Tinkerforge/industrial-dual-ac-in-bricklet/software/src/communication.h

/* industrial-dual-ac-in-bricklet
 * Copyright (C) 2023 Olaf Lüke <olaf@tinkerfoe.com>
 *
 * communication.h: TFP protocol message handling
 *
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
 * You should have received a copy of the GNU Lesser General Public
 * License along with this library; if not, write to the
 * Free Software Foundation, Inc., 59 Temple Place - Suite 330,
 * Boston, MA 02111-1307, USA.
 */

#ifndef COMMUNICATION_H
#define COMMUNICATION_H

#include <stdint.h>
#include <stdbool.h>

#include "bricklib2/protocols/tfp/tfp.h"
#include "bricklib2/bootloader/bootloader.h"

// Default functions
BootloaderHandleMessageResponse handle_message(const void *data, void *response);
void communication_tick(void);
void communication_init(void);

// Constants

#define INDUSTRIAL_DUAL_AC_IN_CHANNEL_0 0
#define INDUSTRIAL_DUAL_AC_IN_CHANNEL_1 1

#define INDUSTRIAL_DUAL_AC_IN_CHANNEL_LED_CONFIG_OFF 0
#define INDUSTRIAL_DUAL_AC_IN_CHANNEL_LED_CONFIG_ON 1
#define INDUSTRIAL_DUAL_AC_IN_CHANNEL_LED_CONFIG_SHOW_HEARTBEAT 2
#define INDUSTRIAL_DUAL_AC_IN_CHANNEL_LED_CONFIG_SHOW_CHANNEL_STATUS 3

#define INDUSTRIAL_DUAL_AC_IN_BOOTLOADER_MODE_BOOTLOADER 0
#define INDUSTRIAL_DUAL_AC_IN_BOOTLOADER_MODE_FIRMWARE 1
#define INDUSTRIAL_DUAL_AC_IN_BOOTLOADER_MODE_BOOTLOADER_WAIT_FOR_REBOOT 2
#define INDUSTRIAL_DUAL_AC_IN_BOOTLOADER_MODE_FIRMWARE_WAIT_FOR_REBOOT 3
#define INDUSTRIAL_DUAL_AC_IN_BOOTLOADER_MODE_FIRMWARE_WAIT_FOR_ERASE_AND_REBOOT 4

#define INDUSTRIAL_DUAL_AC_IN_BOOTLOADER_STATUS_OK 0
#define INDUSTRIAL_DUAL_AC_IN_BOOTLOADER_STATUS_INVALID_MODE 1
#define INDUSTRIAL_DUAL_AC_IN_BOOTLOADER_STATUS_NO_CHANGE 2
#define INDUSTRIAL_DUAL_AC_IN_BOOTLOADER_STATUS_ENTRY_FUNCTION_NOT_PRESENT 3
#define INDUSTRIAL_DUAL_AC_IN_BOOTLOADER_STATUS_DEVICE_IDENTIFIER_INCORRECT 4
#define INDUSTRIAL_DUAL_AC_IN_BOOTLOADER_STATUS_CRC_MISMATCH 5

#define INDUSTRIAL_DUAL_AC_IN_STATUS_LED_CONFIG_OFF 0
#define INDUSTRIAL_DUAL_AC_IN_STATUS_LED_CONFIG_ON 1
#define INDUSTRIAL_DUAL_AC_IN_STATUS_LED_CONFIG_SHOW_HEARTBEAT 2
#define INDUSTRIAL_DUAL_AC_IN_STATUS_LED_CONFIG_SHOW_STATUS 3

// Function and callback IDs and structs
#define FID_GET_VALUE 1
#define FID_SET_VALUE_CALLBACK_CONFIGURATION 2
#define FID_GET_VALUE_CALLBACK_CONFIGURATION 3
#define FID_SET_ALL_VALUE_CALLBACK_CONFIGURATION 4
#define FID_GET_ALL_VALUE_CALLBACK_CONFIGURATION 5
#define FID_SET_CHANNEL_LED_CONFIG 6
#define FID_GET_CHANNEL_LED_CONFIG 7

#define FID_CALLBACK_VALUE 8
#define FID_CALLBACK_ALL_VALUE 9

typedef struct {
	TFPMessageHeader header;
} __attribute__((__packed__)) GetValue;

typedef struct {
	TFPMessageHeader header;
	uint8_t value[1];
} __attribute__((__packed__)) GetValue_Response;

typedef struct {
	TFPMessageHeader header;
	uint8_t channel;
	uint32_t period;
	bool value_has_to_change;
} __attribute__((__packed__)) SetValueCallbackConfiguration;

typedef struct {
	TFPMessageHeader header;
	uint8_t channel;
} __attribute__((__packed__)) GetValueCallbackConfiguration;

typedef struct {
	TFPMessageHeader header;
	uint32_t period;
	bool value_has_to_change;
} __attribute__((__packed__)) GetValueCallbackConfiguration_Response;

typedef struct {
	TFPMessageHeader header;
	uint32_t period;
	bool value_has_to_change;
} __attribute__((__packed__)) SetAllValueCallbackConfiguration;

typedef struct {
	TFPMessageHeader header;
} __attribute__((__packed__)) GetAllValueCallbackConfiguration;

typedef struct {
	TFPMessageHeader header;
	uint32_t period;
	bool value_has_to_change;
} __attribute__((__packed__)) GetAllValueCallbackConfiguration_Response;

typedef struct {
	TFPMessageHeader header;
	uint8_t channel;
	uint8_t config;
} __attribute__((__packed__)) SetChannelLEDConfig;

typedef struct {
	TFPMessageHeader header;
	uint8_t channel;
} __attribute__((__packed__)) GetChannelLEDConfig;

typedef struct {
	TFPMessageHeader header;
	uint8_t config;
} __attribute__((__packed__)) GetChannelLEDConfig_Response;

typedef struct {
	TFPMessageHeader header;
	uint8_t channel;
	bool changed;
	bool value;
} __attribute__((__packed__)) Value_Callback;

typedef struct {
	TFPMessageHeader header;
	uint8_t changed[1];
	uint8_t value[1];
} __attribute__((__packed__)) AllValue_Callback;


// Function prototypes
BootloaderHandleMessageResponse get_value(const GetValue *data, GetValue_Response *response);
BootloaderHandleMessageResponse set_value_callback_configuration(const SetValueCallbackConfiguration *data);
BootloaderHandleMessageResponse get_value_callback_configuration(const GetValueCallbackConfiguration *data, GetValueCallbackConfiguration_Response *response);
BootloaderHandleMessageResponse set_all_value_callback_configuration(const SetAllValueCallbackConfiguration *data);
BootloaderHandleMessageResponse get_all_value_callback_configuration(const GetAllValueCallbackConfiguration *data, GetAllValueCallbackConfiguration_Response *response);
BootloaderHandleMessageResponse set_channel_led_config(const SetChannelLEDConfig *data);
BootloaderHandleMessageResponse get_channel_led_config(const GetChannelLEDConfig *data, GetChannelLEDConfig_Response *response);

// Callbacks
bool handle_value_callback(void);
bool handle_all_value_callback(void);

#define COMMUNICATION_CALLBACK_TICK_WAIT_MS 1
#define COMMUNICATION_CALLBACK_HANDLER_NUM 2
#define COMMUNICATION_CALLBACK_LIST_INIT \
	handle_value_callback, \
	handle_all_value_callback, \


#endif
